WellsWang/TERM64/Model_25/Images/P1.png

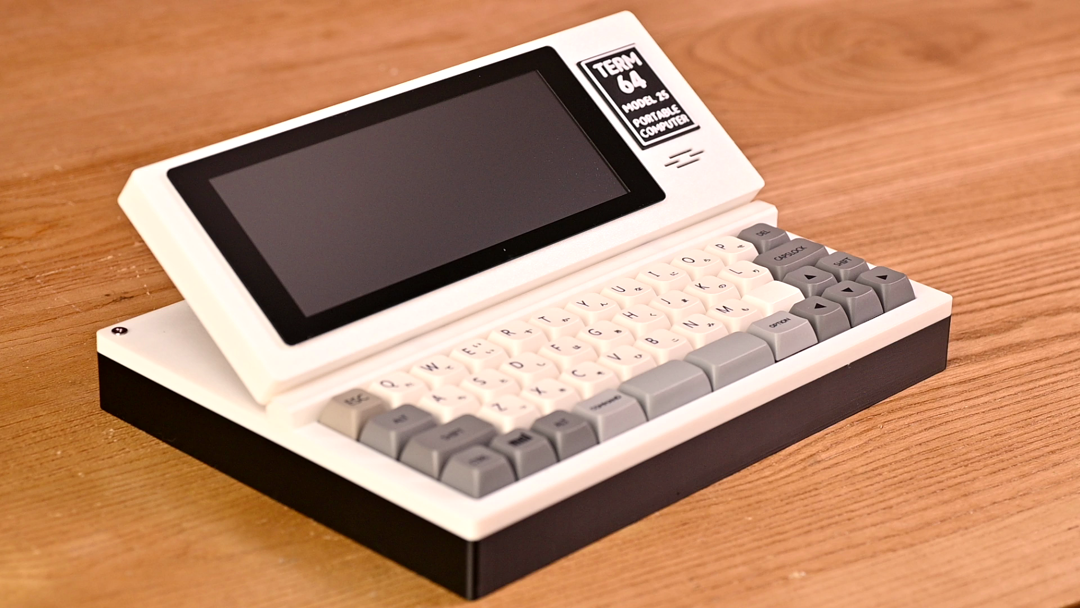
Model_25/Images/P1.png
